74th/tv-side-keyboard-SparrowTV/firmware-circuitpython/settings.py

import board

IR_OUT_PIN = board.IO1
IR_IN_PIN = board.IO0

I2C_SDA_PIN = board.IO2
I2C_SCL_PIN = board.IO3

CH9329_TX = board.IO7
CH9329_RX = board.IO6

MATRIX_LED_PIN = board.IO4

MATRIX_COL_NUM = 5
MATRIX_ROW_NUM = 3

MATRIX_BUTTON_MAP = [[0, 1, 2, 3, 4], [5, 6, 7, 8, 9], [10, 11, 12, 13, 14]]

MATRIX_LED_NUM = 15
MATRIX_LED_MAP = [[0, 1, 2, 3, 4], [5, 6, 7, 8, 9], [10, 11, 12, 13, 14]]

POINTER_DEVICE_ADDR = 0x0A
