74th/tv-side-keyboard-SparrowTV/firmware-circuitpython/led_color.py

from model import LEDColor

L_RED = (0x00, 0x10, 0x00)
L_BLUE = (0x00, 0x00, 0x10)
L_GREEN = (0x10, 0x00, 0x00)

L_YELLOW = (0x10, 0x10, 0x00)
L_CYAN = (0x10, 0x00, 0x10)
L_PURPLE = (0x00, 0x10, 0x10)

L_WHITE = (0x10, 0x10, 0x10)

L_BLACK = (0x00, 0x00, 0x00)
