74th/tv-side-keyboard-SparrowTV/firmware-circuitpython/color.py

from matrix_leds import LEDColor

# g, r, b
CL_WHITE: LEDColor = (0xF0, 0xF0, 0xF0)
CL_NONE: LEDColor = (0x00, 0x00, 0x00)
CL_RED: LEDColor = (0x00, 0xF0, 0x00)
CL_GREEN: LEDColor = (0xF0, 0x00, 0x00)
CL_BLUE: LEDColor = (0x00, 0x00, 0xF0)
